hjy2664174646/Wheel_legged_Robot/solidworks/机加工图纸及模型/lvguan-3.stp

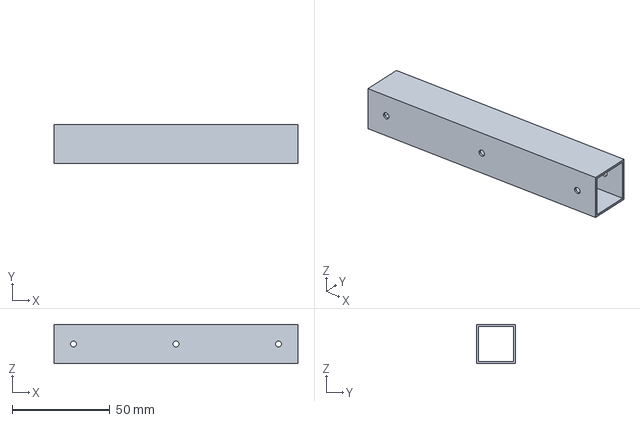
[picture p16: CAD file, 2026-09-19]
solidworks/机加工图纸及模型/lvguan-3.stp
125.0 x 20.0 x 20.0 mm
