hjy2664174646/Wheel_legged_Robot/solidworks/hhu外壳改版sw/电池仓.SLDPRT

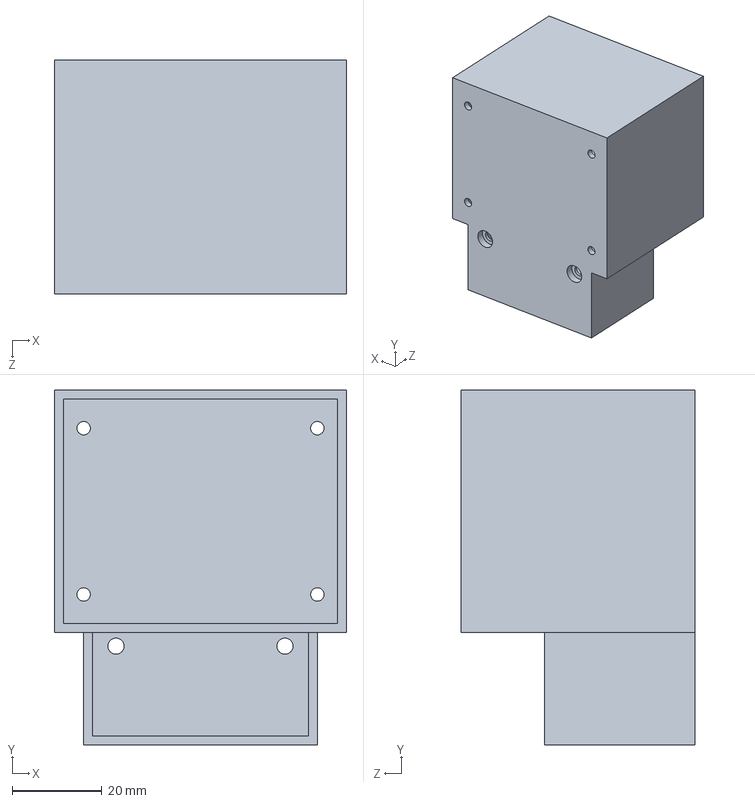
[picture p18: CAD file, 2026-09-19]
solidworks/hhu外壳改版sw/电池仓.SLDPRT
65.0 x 79.0 x 52.0 mm
