hjy2664174646/Wheel_legged_Robot/fishbot_ws/src/wheel_legged_urdf_pkg/meshes/imu_link.STL

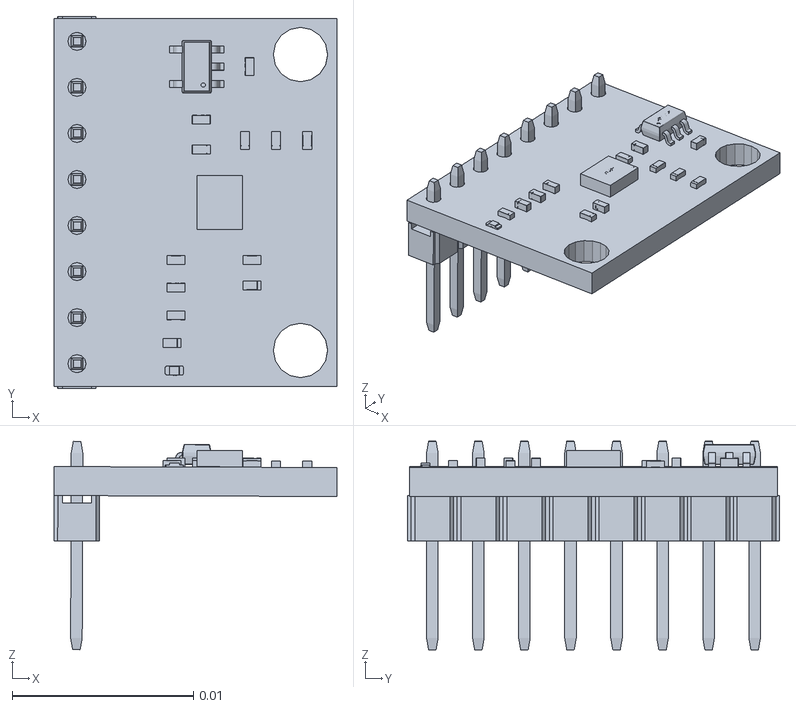
[picture p20: CAD file, 2026-06-02]
fishbot_ws/src/wheel_legged_urdf_pkg/meshes/imu_link.STL
0.0156 x 0.0205 x 0.0115
