hjy2664174646/Wheel_legged_Robot/solidworks/机加工图纸及模型/banjiejian-2.stp

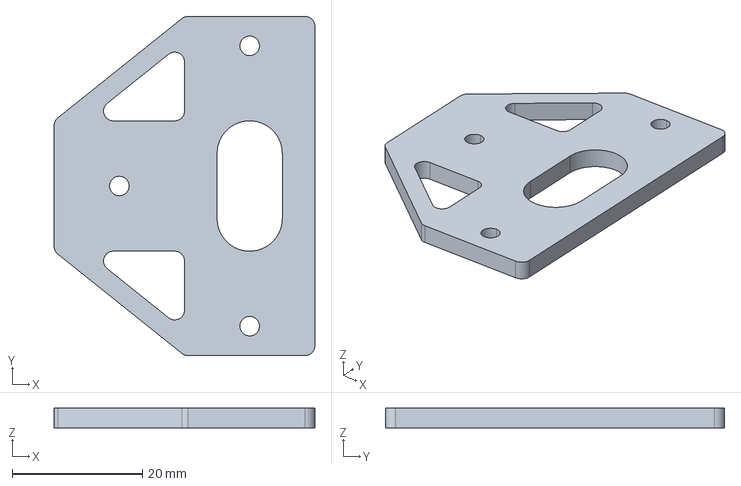
[picture p21: CAD file, 2026-09-19]
solidworks/机加工图纸及模型/banjiejian-2.stp
40.0 x 52.0 x 3.00 mm
