hjy2664174646/Wheel_legged_Robot/solidworks/hhu外壳改版sw/摄像头支架.SLDPRT

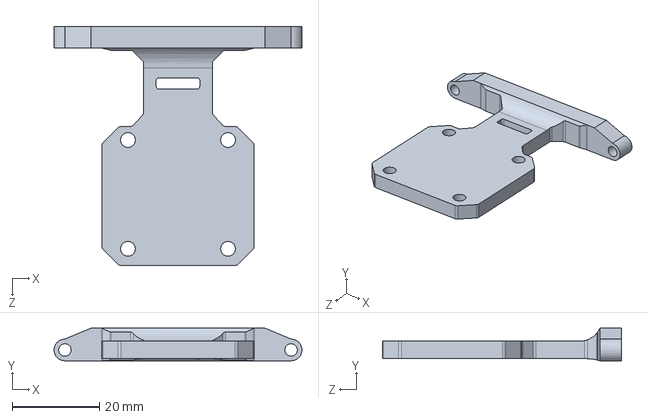
[picture p22: CAD file, 2026-09-19]
solidworks/hhu外壳改版sw/摄像头支架.SLDPRT
57.0 x 7.50 x 55.0 mm
