hjy2664174646/Wheel_legged_Robot/solidworks/机加工图纸及模型/lianjieban-1.stp

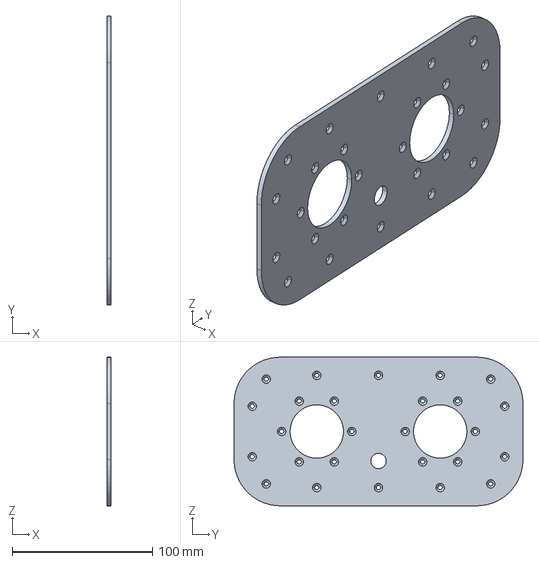
[picture p23: CAD file, 2026-09-19]
solidworks/机加工图纸及模型/lianjieban-1.stp
3.00 x 206.0 x 106.0 mm
