hjy2664174646/Wheel_legged_Robot/solidworks/hhu外壳改版sw/前盖板（带开关充电口）.SLDPRT

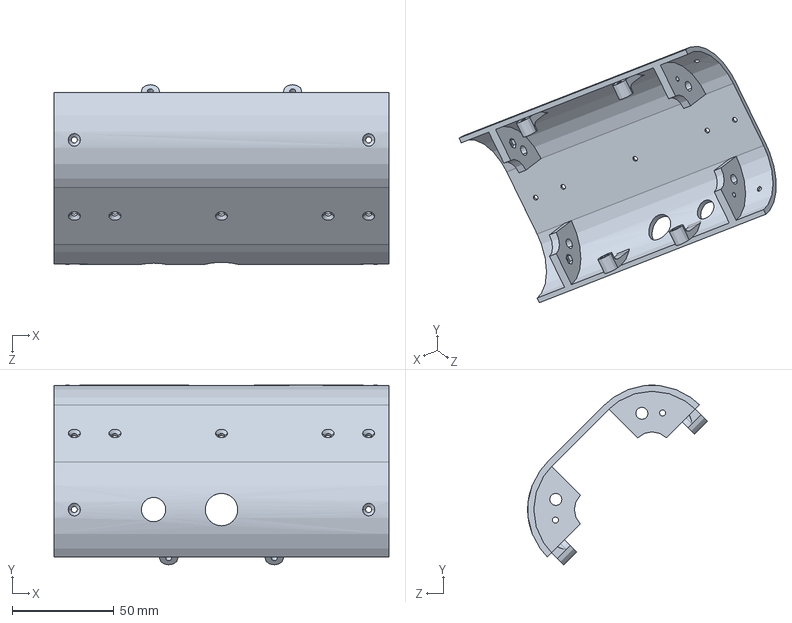
[picture p25: CAD file, 2026-09-19]
solidworks/hhu外壳改版sw/前盖板（带开关充电口）.SLDPRT
165.0 x 88.5 x 88.5 mm
