hjy2664174646/Wheel_legged_Robot/solidworks/机加工图纸及模型/lvguan-1.stp

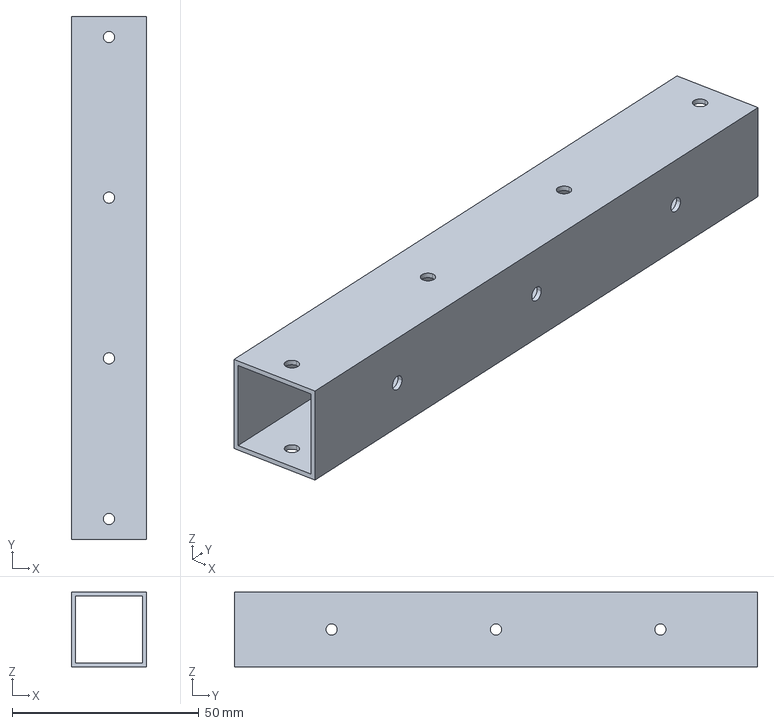
[picture p26: CAD file, 2026-09-19]
solidworks/机加工图纸及模型/lvguan-1.stp
20.0 x 140.0 x 20.0 mm
