hjy2664174646/Wheel_legged_Robot/fishbot_ws/src/wheel_legged_urdf_pkg/meshes/left_l1_link.STL

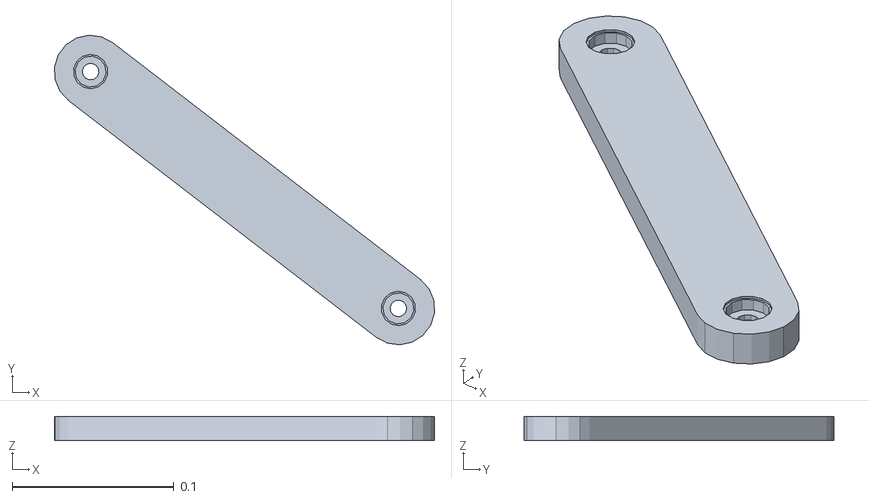
[picture p27: CAD file, 2026-06-02]
fishbot_ws/src/wheel_legged_urdf_pkg/meshes/left_l1_link.STL
0.235 x 0.191 x 0.015
