hjy2664174646/Wheel_legged_Robot/solidworks/hhu外壳改版sw/N10雷达支架（抬高）.SLDPRT

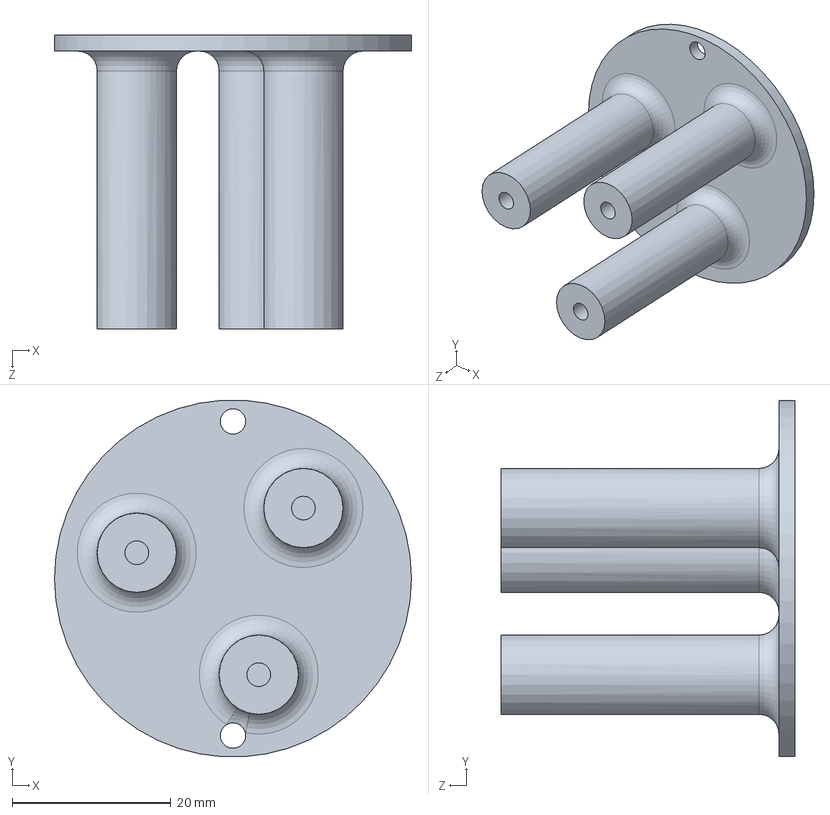
[picture p28: CAD file, 2026-09-19]
solidworks/hhu外壳改版sw/N10雷达支架（抬高）.SLDPRT
45.0 x 44.9 x 37.0 mm
