hjy2664174646/Wheel_legged_Robot/solidworks/机加工图纸及模型/liangna4.dxf

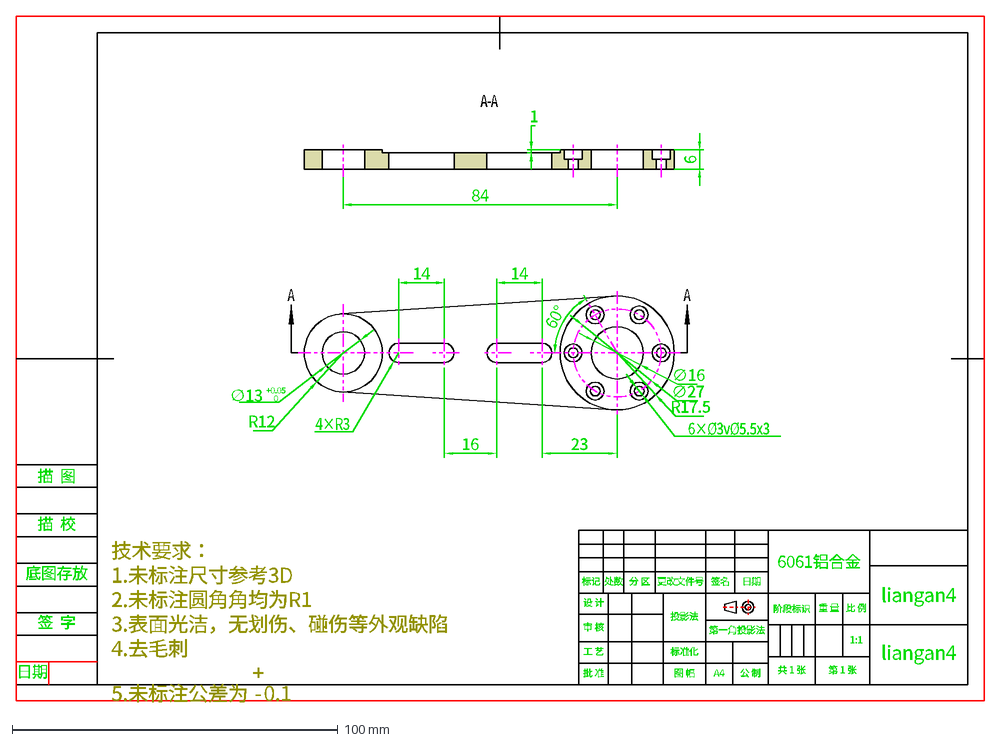
[picture p29: CAD file, 2026-09-19]
solidworks/机加工图纸及模型/liangna4.dxf
日期
签 字
底图存放
描 校
描 图
6061铝合金
liangan4
标记
处数
分 区
更改文件号
签名
设 计
投影法
阶段标识
重 量
比 例
审 核
第一角投影法
1:1
工 艺
标准化
共 1 张
第 1 张
批 准
图 幅
A4
公 制
技术要求： 1.未标注尺寸参考3D 2.未标注圆角角均为R1 3.表面光洁，无划伤、碰伤等外观缺陷 4.去毛刺 5.未标注公差为 +^-0.1
A-A
∅13 +0.05^0
∅16
R12
R17.5
84
∅27
60°
23
14
16
6
1
A
