hjy2664174646/Wheel_legged_Robot/fishbot_ws/src/wheel_legged_urdf_pkg/meshes/right_l4_link.STL

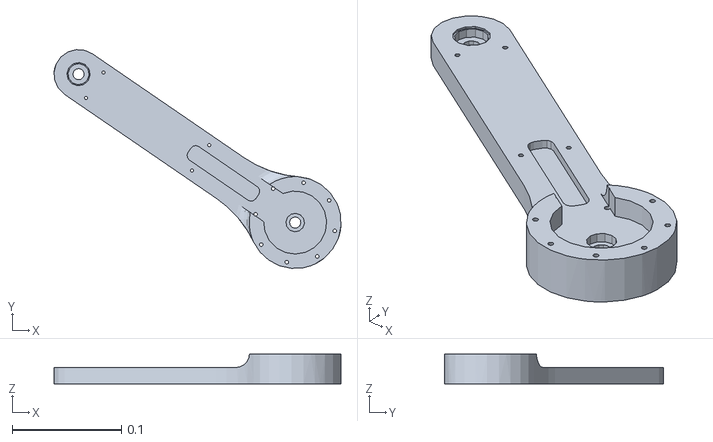
[picture p30: CAD file, 2026-06-02]
fishbot_ws/src/wheel_legged_urdf_pkg/meshes/right_l4_link.STL
0.262 x 0.2 x 0.027
