hjy2664174646/Wheel_legged_Robot/solidworks/机加工图纸及模型/diban-1.stp

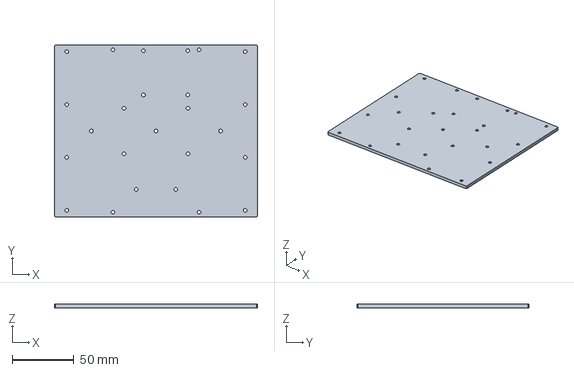
[picture p31: CAD file, 2026-09-19]
solidworks/机加工图纸及模型/diban-1.stp
165.0 x 140.0 x 3.00 mm
