hjy2664174646/Wheel_legged_Robot/solidworks/机加工图纸及模型/dingban.stp

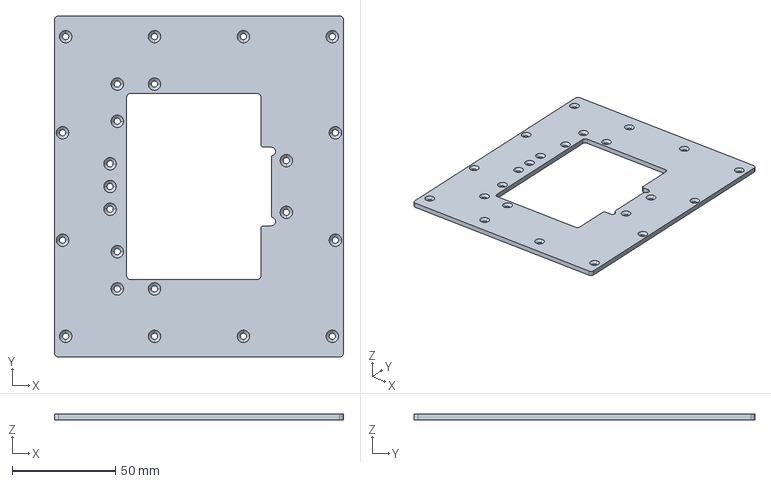
[picture p32: CAD file, 2026-09-19]
solidworks/机加工图纸及模型/dingban.stp
140.0 x 165.0 x 3.00 mm
