hjy2664174646/Wheel_legged_Robot/solidworks/机加工图纸及模型/dinggai.stp

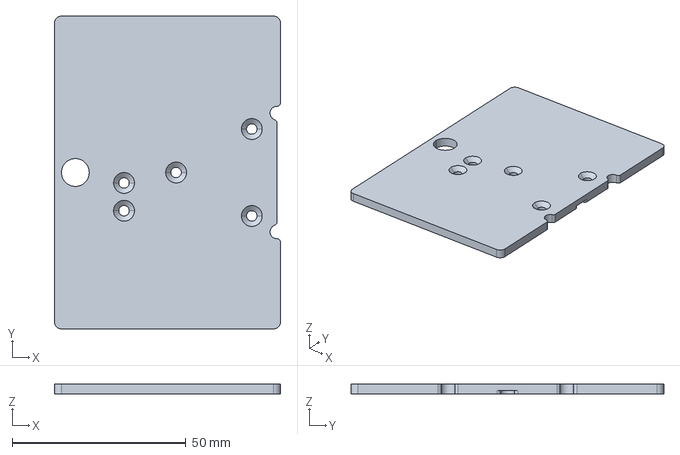
[picture p33: CAD file, 2026-09-19]
solidworks/机加工图纸及模型/dinggai.stp
65.0 x 90.0 x 3.00 mm
