hjy2664174646/Wheel_legged_Robot/fishbot_ws/src/wheel_legged_urdf_pkg/meshes/right_back_motor_link.STL

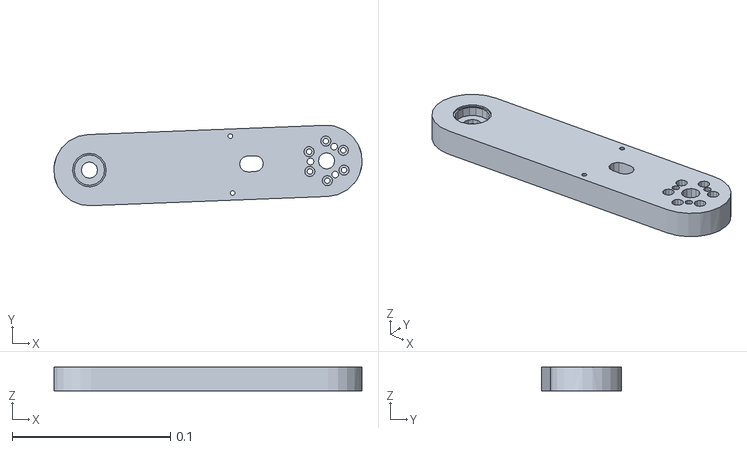
[picture p34: CAD file, 2026-06-02]
fishbot_ws/src/wheel_legged_urdf_pkg/meshes/right_back_motor_link.STL
0.195 x 0.0508 x 0.015
