hjy2664174646/Wheel_legged_Robot/solidworks/机加工图纸及模型/banjiejian-1.stp

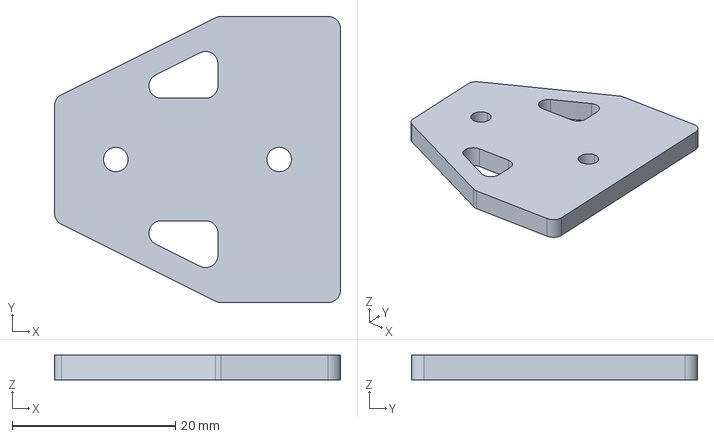
[picture p35: CAD file, 2026-09-19]
solidworks/机加工图纸及模型/banjiejian-1.stp
35.0 x 35.0 x 3.00 mm
