hjy2664174646/Wheel_legged_Robot/solidworks/机加工图纸及模型/lvguan-2.stp

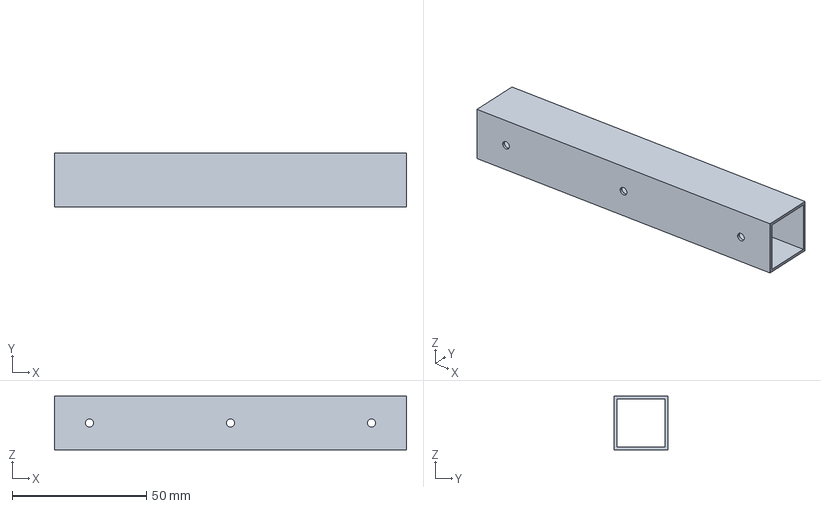
[picture p36: CAD file, 2026-09-19]
solidworks/机加工图纸及模型/lvguan-2.stp
131.0 x 20.0 x 20.0 mm
